lukasznowarkiewicz/3dCane/hardware-mechanical/accessories/uchwyt scienny do laski z miejscem na przewod do ladowania.png

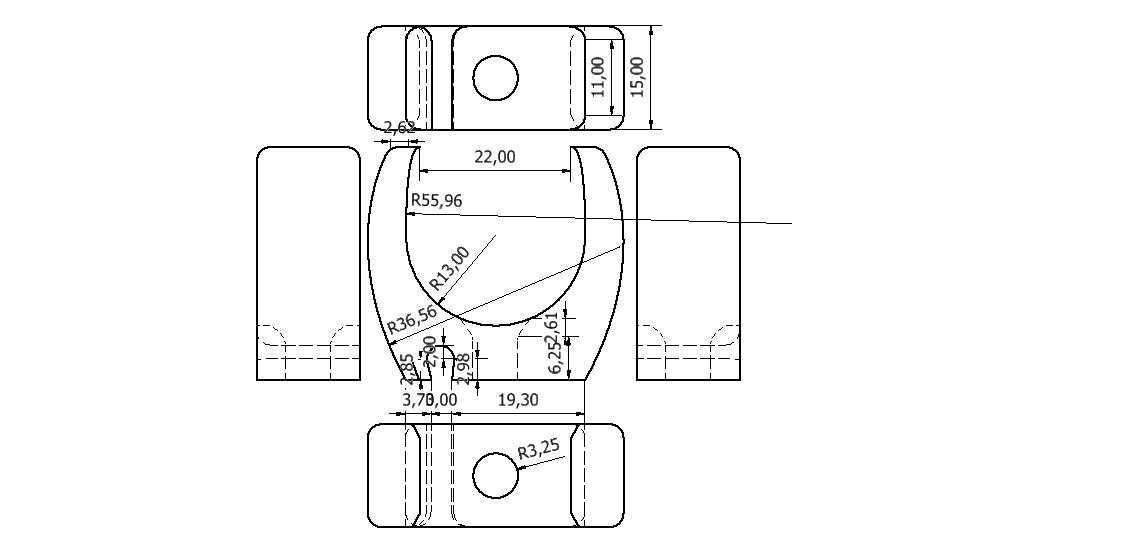
hardware-mechanical/accessories/uchwyt scienny do laski z miejscem na przewod do ladowania.png
