lukasznowarkiewicz/3dCane/hardware-mechanical/accessories/uchwyt scienny do laski.png

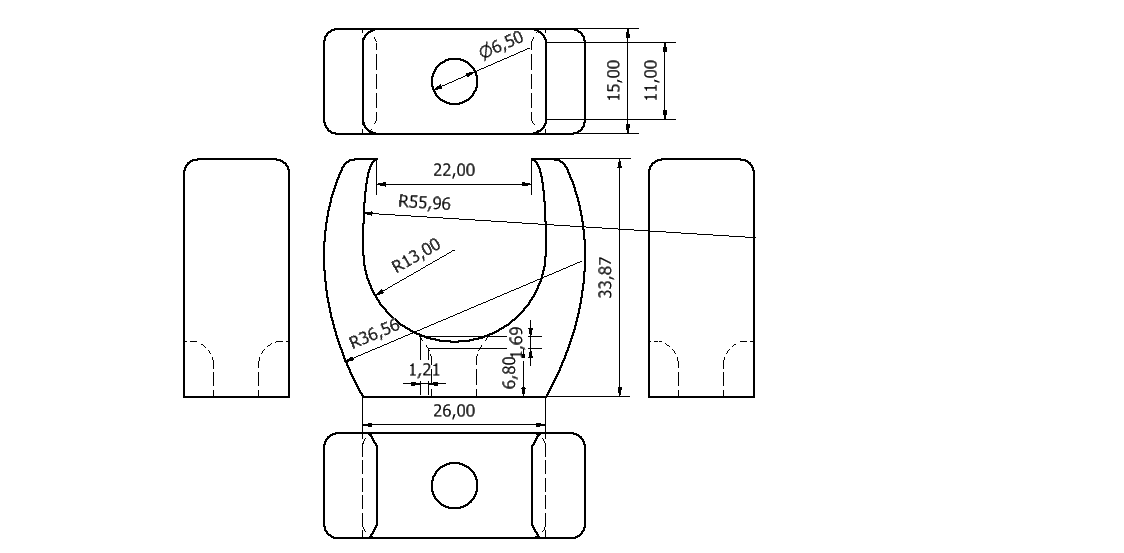
hardware-mechanical/accessories/uchwyt scienny do laski.png
