lukasznowarkiewicz/3dCane/hardware-mechanical/accessories/ˆadowarka usb v2 przykrywka.png

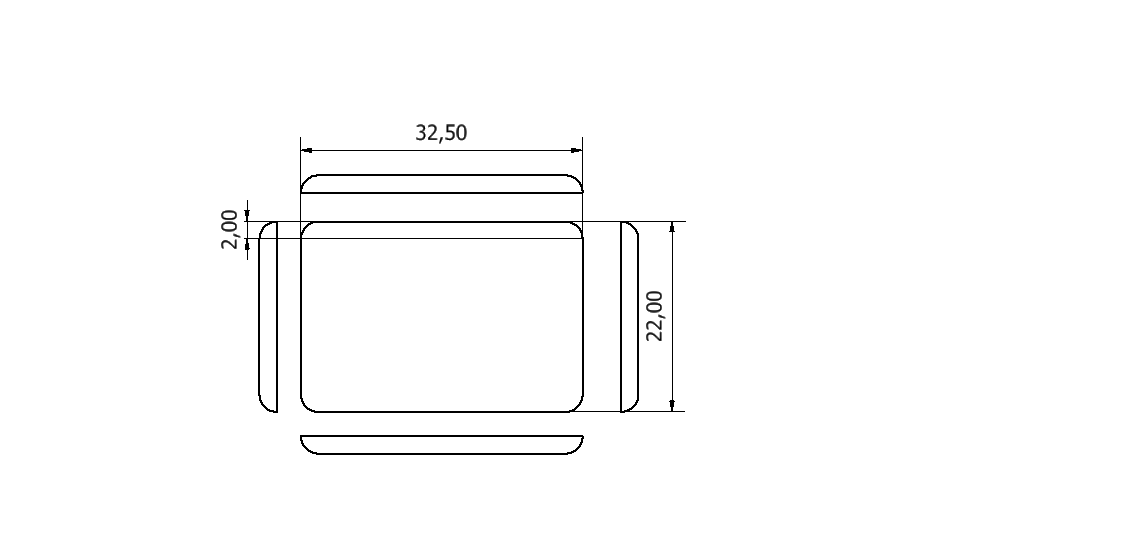
hardware-mechanical/accessories/ˆadowarka usb v2 przykrywka.png
