lukasznowarkiewicz/3dCane/hardware-mechanical/accessories/ˆadowarka usb v2-.png

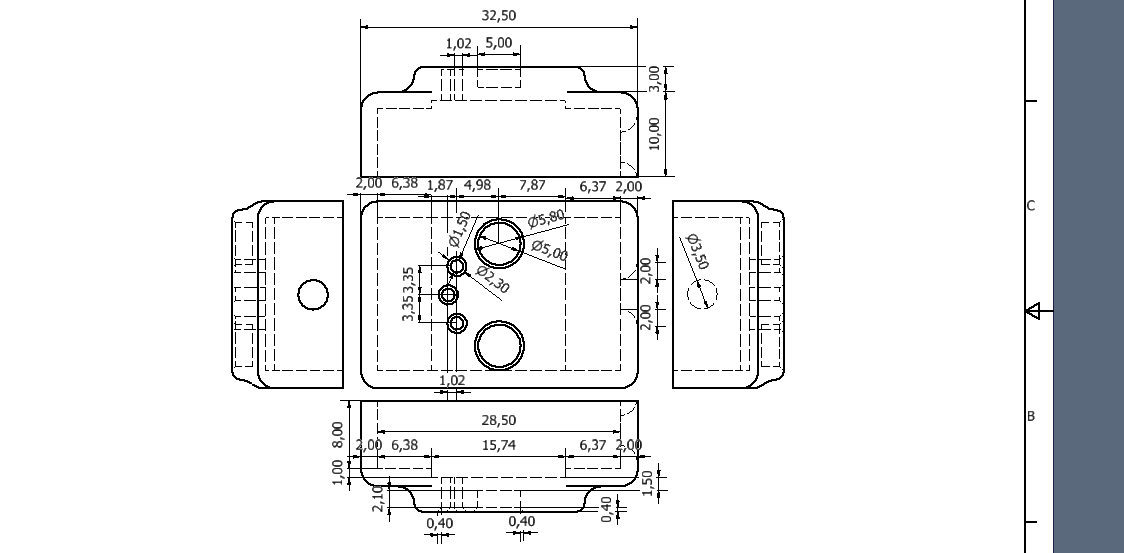
hardware-mechanical/accessories/ˆadowarka usb v2-.png
