lukasznowarkiewicz/3dCane/hardware-mechanical/cane/koncowka do laski - kula.png

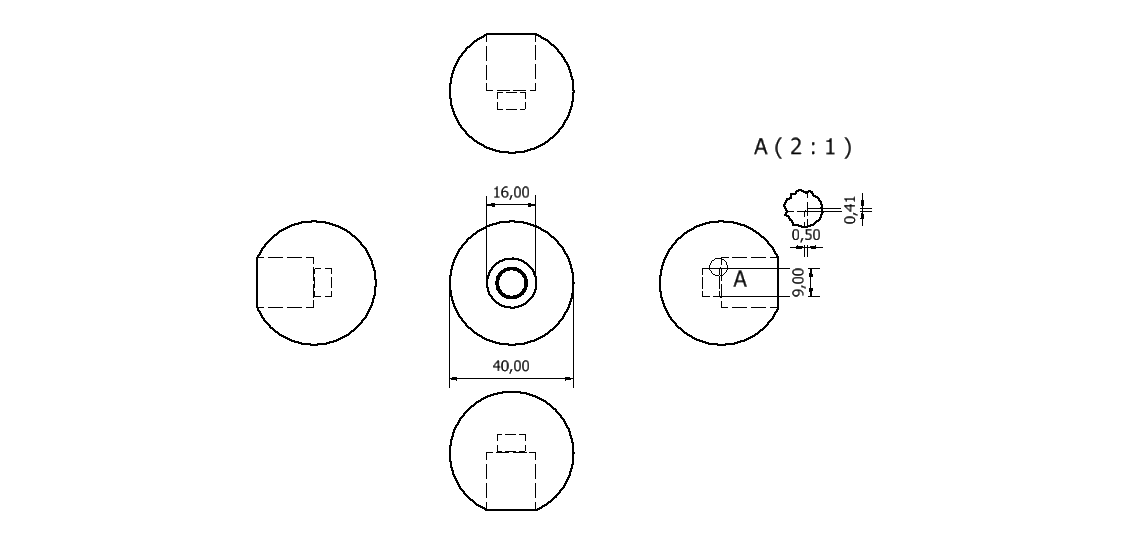
hardware-mechanical/cane/koncowka do laski - kula.png
