lukasznowarkiewicz/3dCane/hardware-mechanical/cane/koncowka z miejscem na magnes neodymowy 7x7x3.png

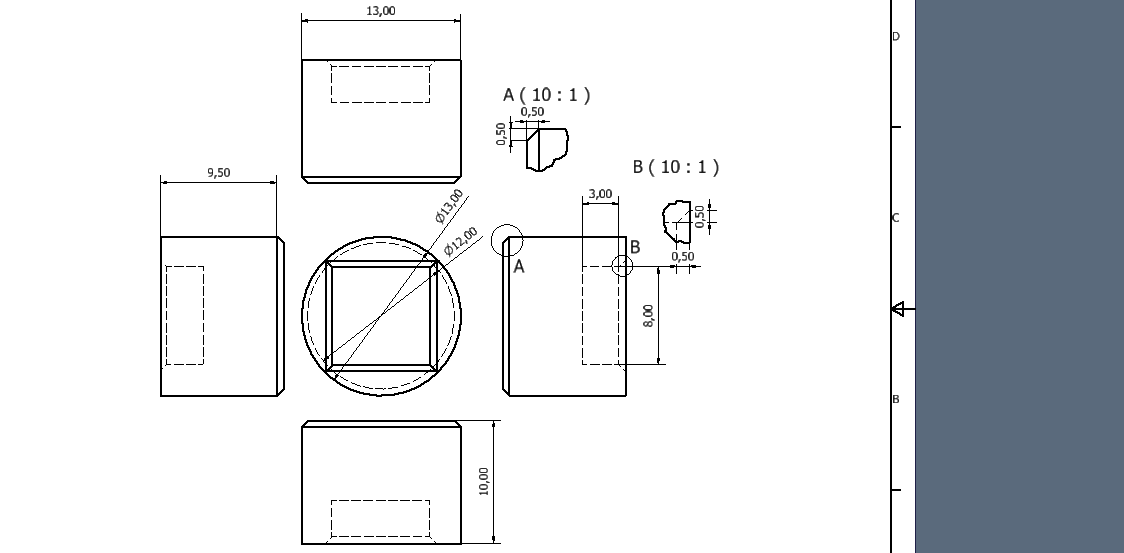
hardware-mechanical/cane/koncowka z miejscem na magnes neodymowy 7x7x3.png
