lukasznowarkiewicz/3dCane/hardware-mechanical/cane/obudowa do czujnikow odleglosci v3,2 - przykrywka.png

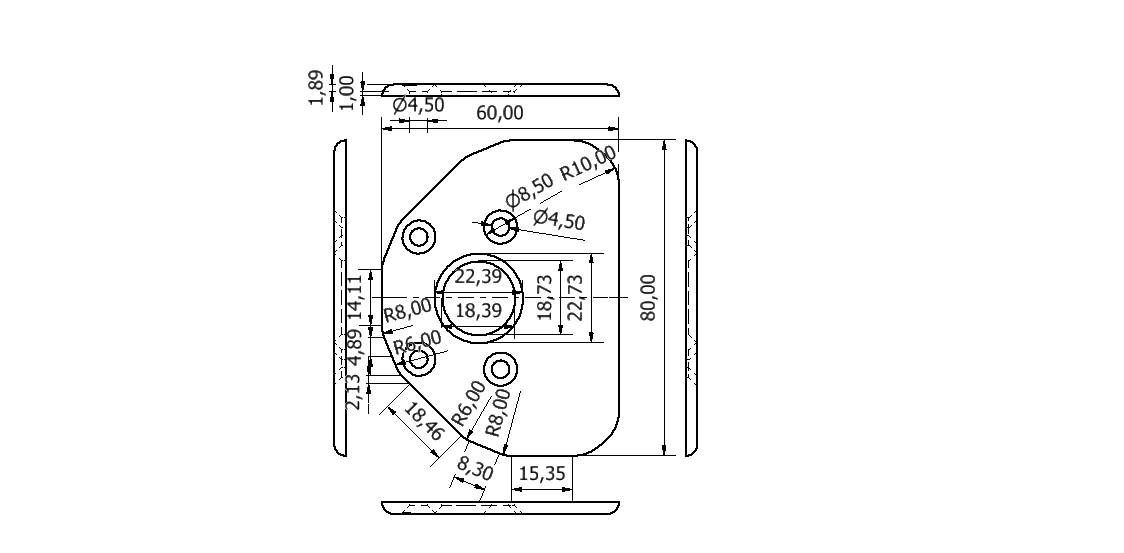
hardware-mechanical/cane/obudowa do czujnikow odleglosci v3,2 - przykrywka.png
