lukasznowarkiewicz/3dCane/hardware-mechanical/cane/obudowa do czujnikow odleglosci v3,2.bmp

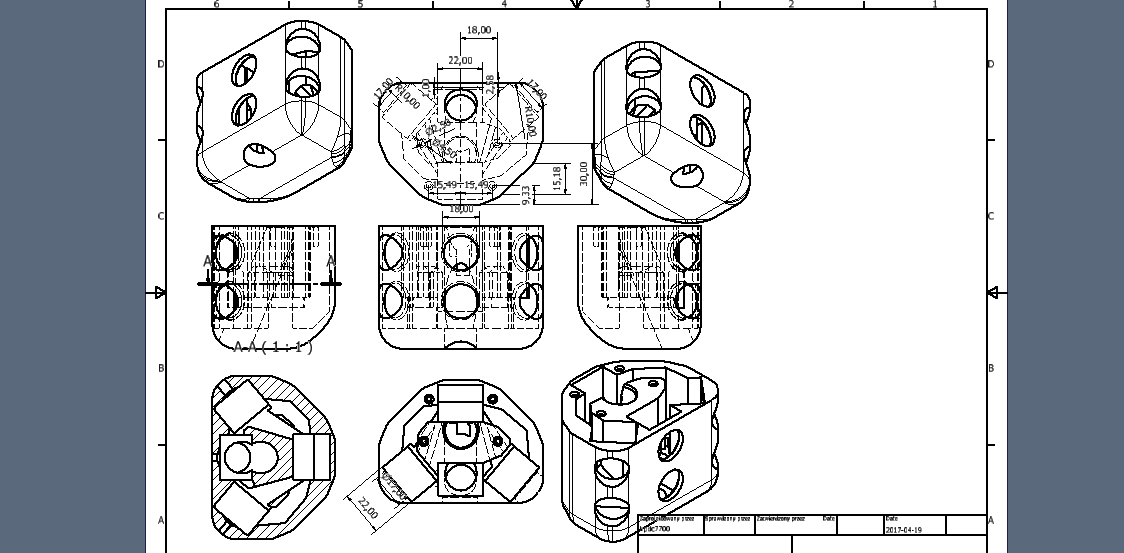
hardware-mechanical/cane/obudowa do czujnikow odleglosci v3,2.bmp
