lukasznowarkiewicz/3dCane/hardware-mechanical/cane/pierscien rurka cienka.png

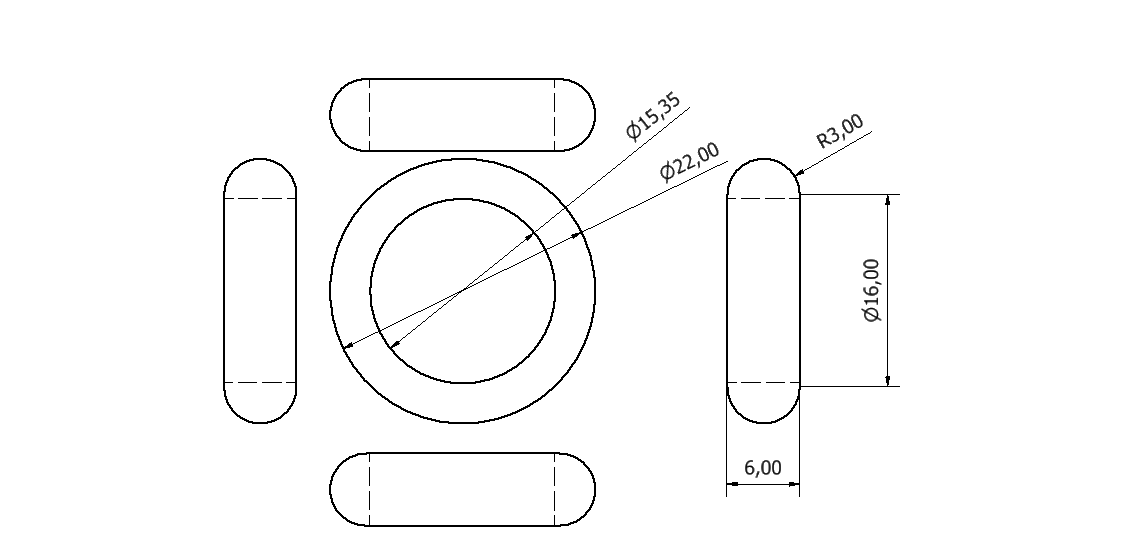
hardware-mechanical/cane/pierscien rurka cienka.png
