lukasznowarkiewicz/3dCane/hardware-mechanical/cane/raczka do laski ver 5.png

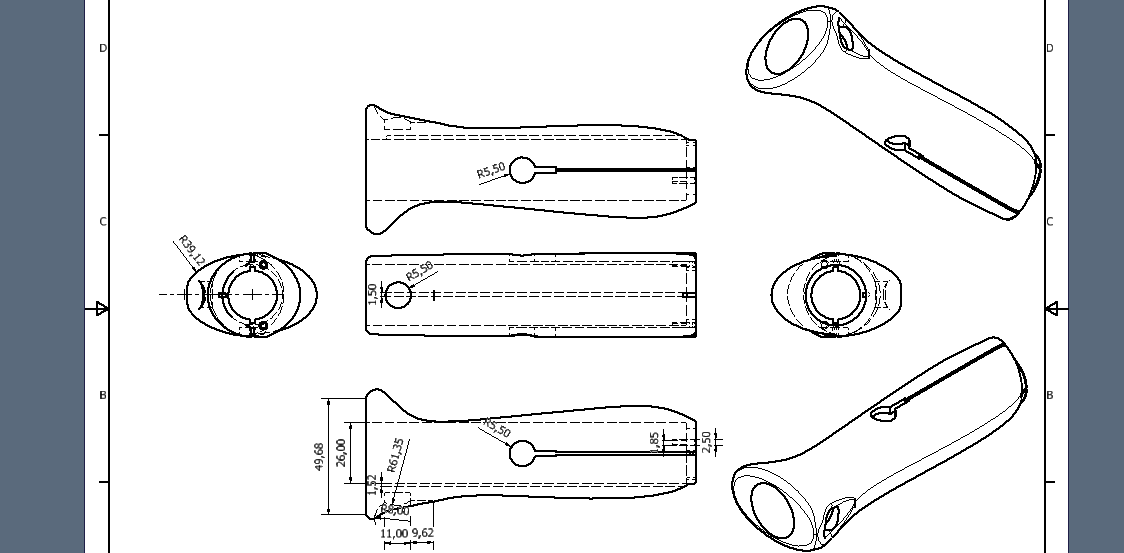
hardware-mechanical/cane/raczka do laski ver 5.png
