lukasznowarkiewicz/3dCane/hardware-mechanical/cane/zatyczka do raczki.png

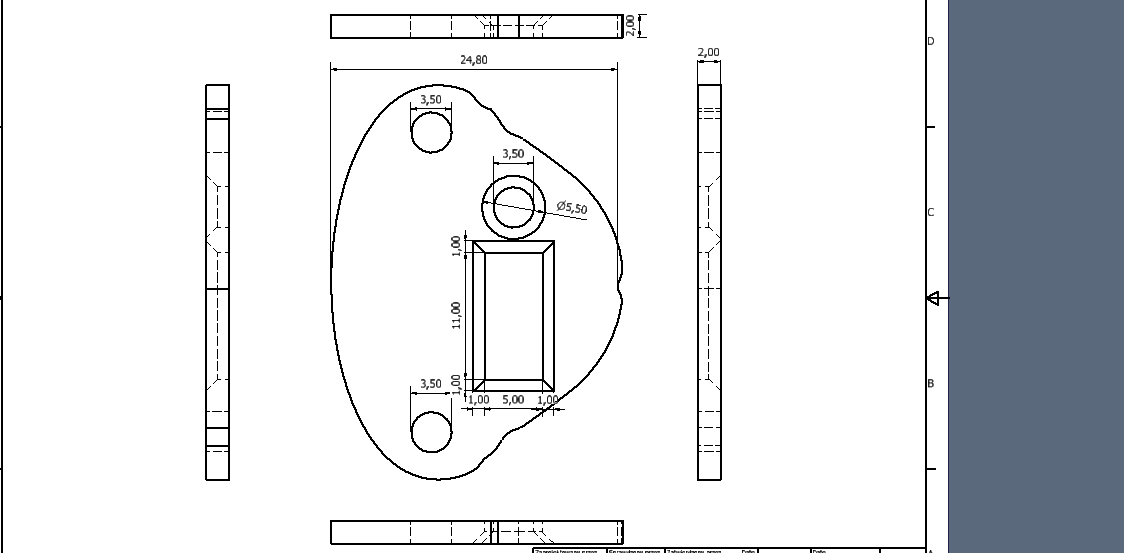
hardware-mechanical/cane/zatyczka do raczki.png
