lukasznowarkiewicz/3dCane/hardware-mechanical/screenshots/Screenshot_1.png

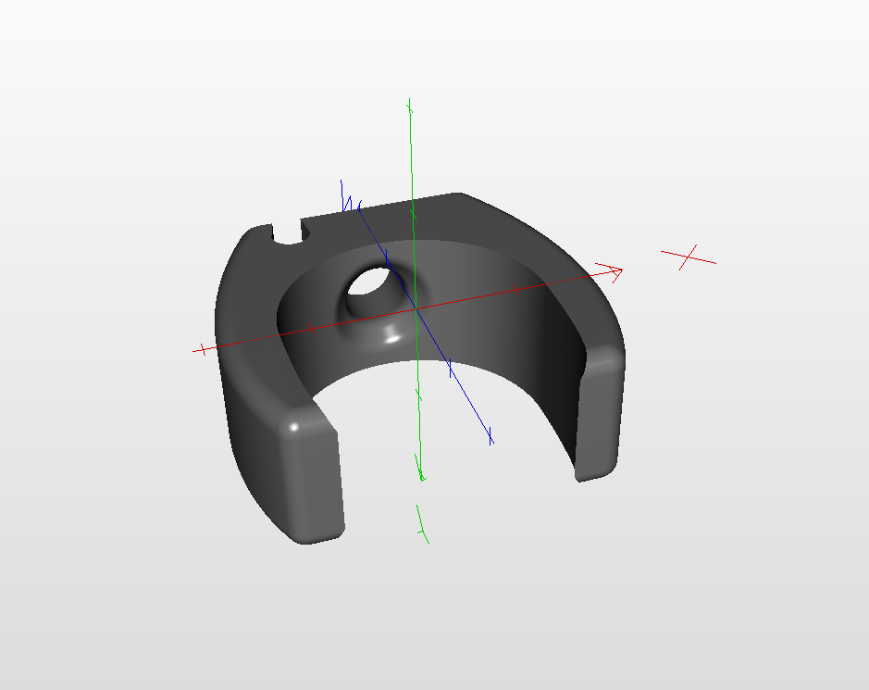
hardware-mechanical/screenshots/Screenshot_1.png
