lukasznowarkiewicz/3dCane/hardware-mechanical/screenshots/Screenshot_2.png

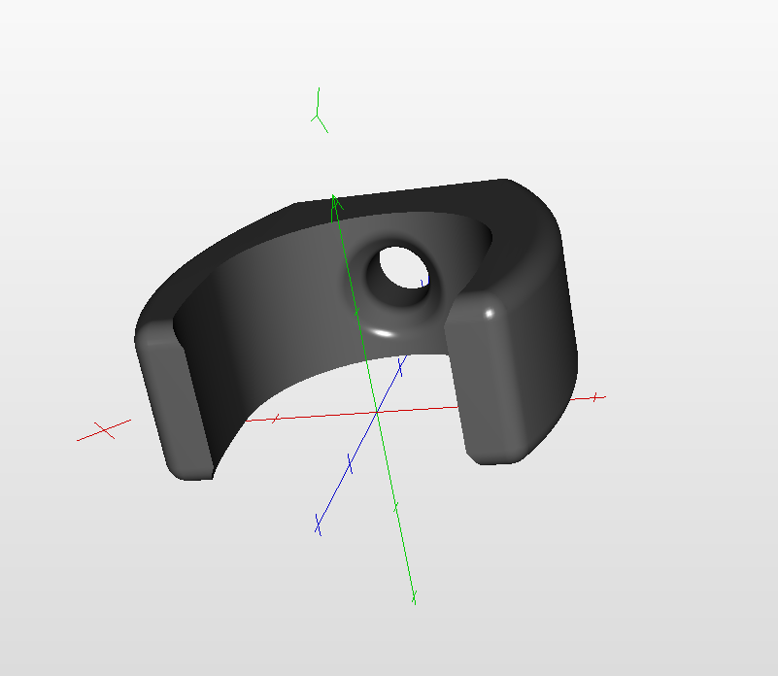
hardware-mechanical/screenshots/Screenshot_2.png
