lukasznowarkiewicz/3dCane/hardware-mechanical/screenshots/Screenshot_3.png

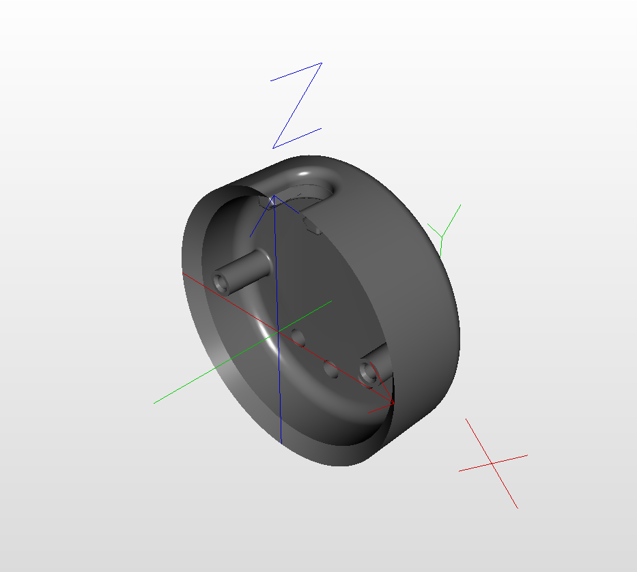
hardware-mechanical/screenshots/Screenshot_3.png
