lukasznowarkiewicz/3dCane/hardware-mechanical/screenshots/Screenshot_4.png

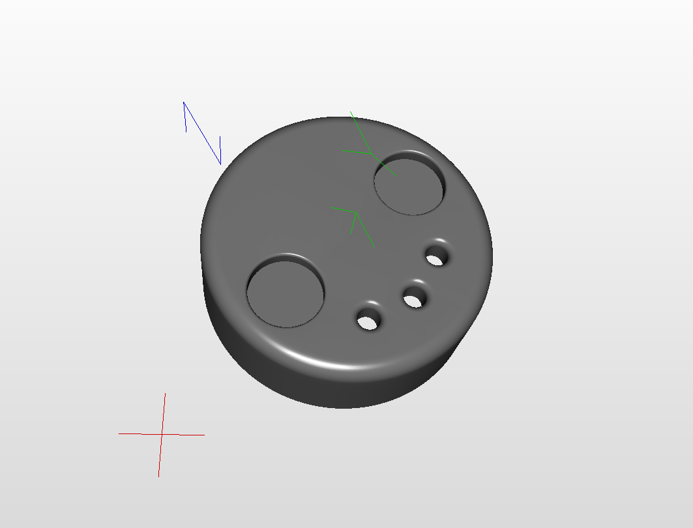
hardware-mechanical/screenshots/Screenshot_4.png
