lukasznowarkiewicz/3dCane/hardware-mechanical/screenshots/Screenshot_5.png

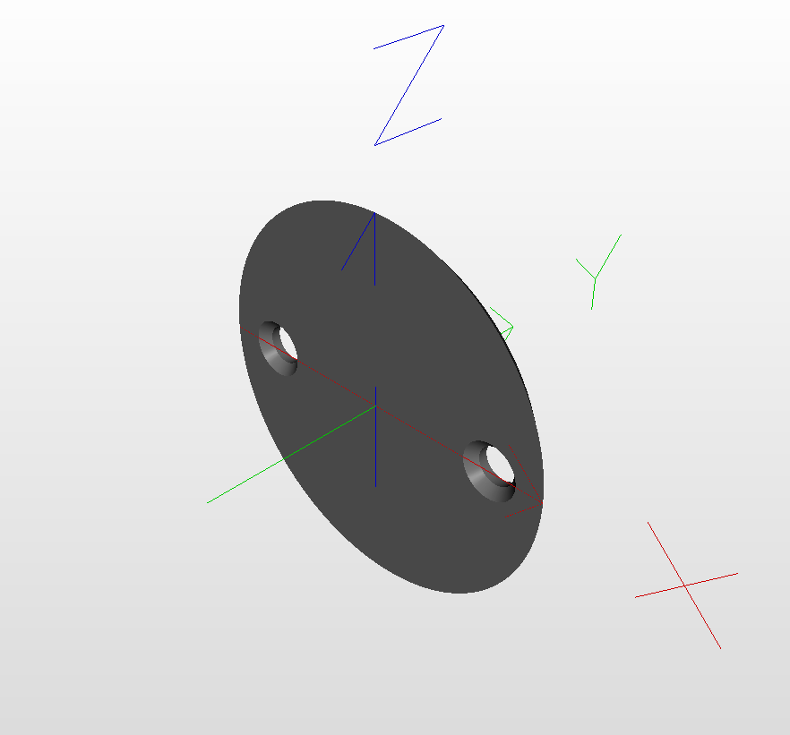
hardware-mechanical/screenshots/Screenshot_5.png
