lukasznowarkiewicz/3dCane/hardware-mechanical/screenshots/Screenshot_6.png

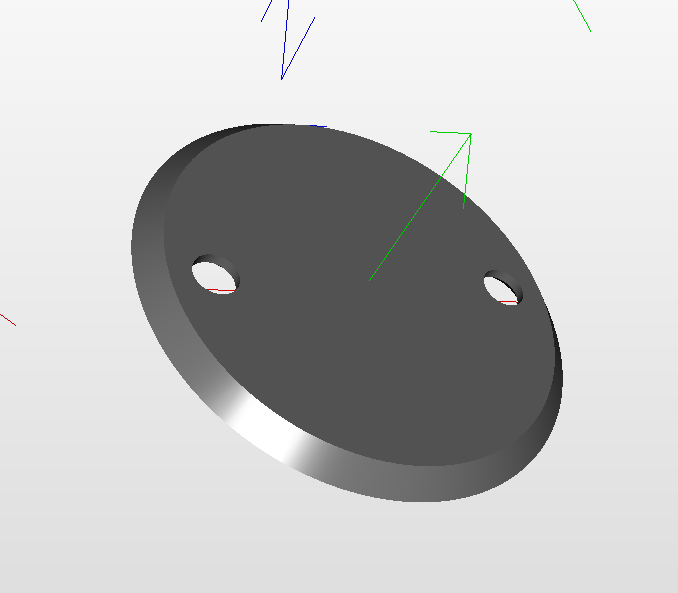
hardware-mechanical/screenshots/Screenshot_6.png
