lukasznowarkiewicz/3dCane/hardware-mechanical/screenshots/Screenshot_8.png

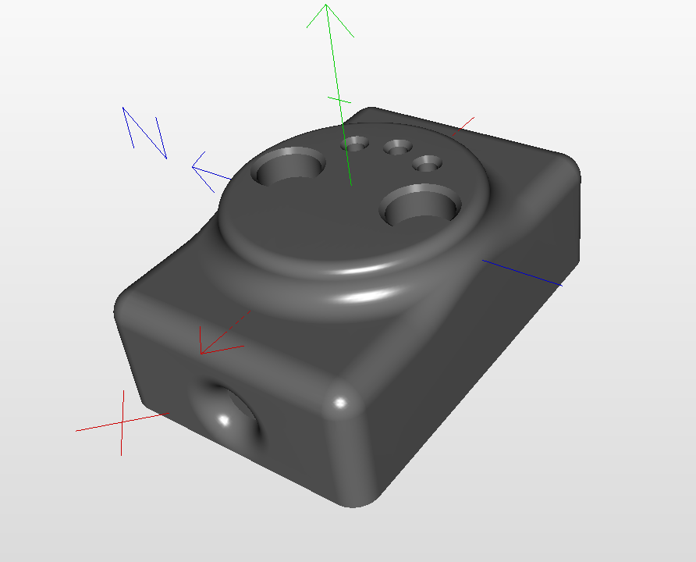
hardware-mechanical/screenshots/Screenshot_8.png
