lukasznowarkiewicz/3dCane/hardware-mechanical/screenshots/Screenshot_10.png

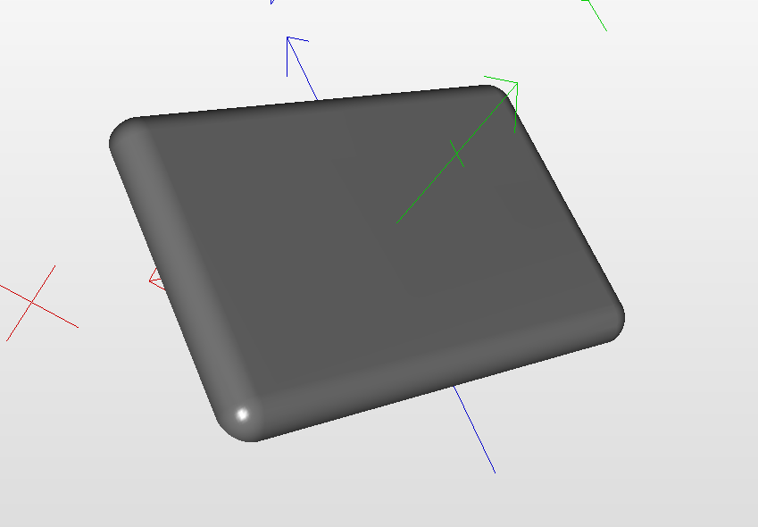
hardware-mechanical/screenshots/Screenshot_10.png
