lukasznowarkiewicz/3dCane/hardware-mechanical/screenshots/Screenshot_12.png

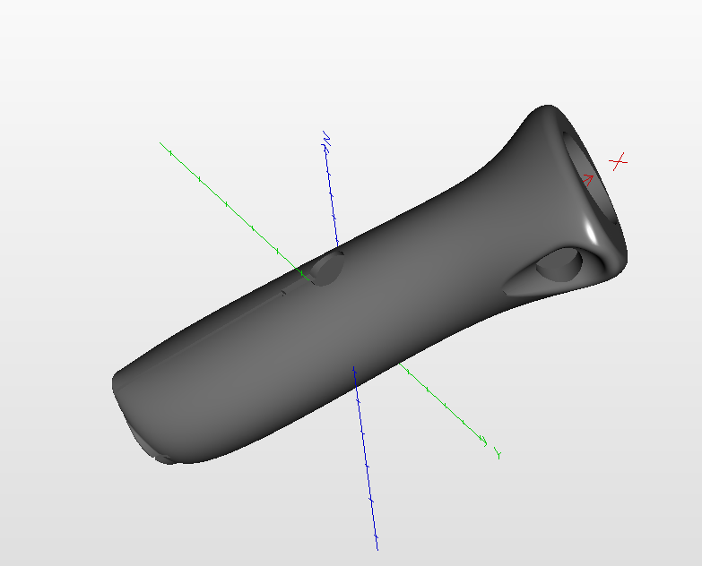
hardware-mechanical/screenshots/Screenshot_12.png
