lukasznowarkiewicz/3dCane/hardware-mechanical/screenshots/Screenshot_13.png

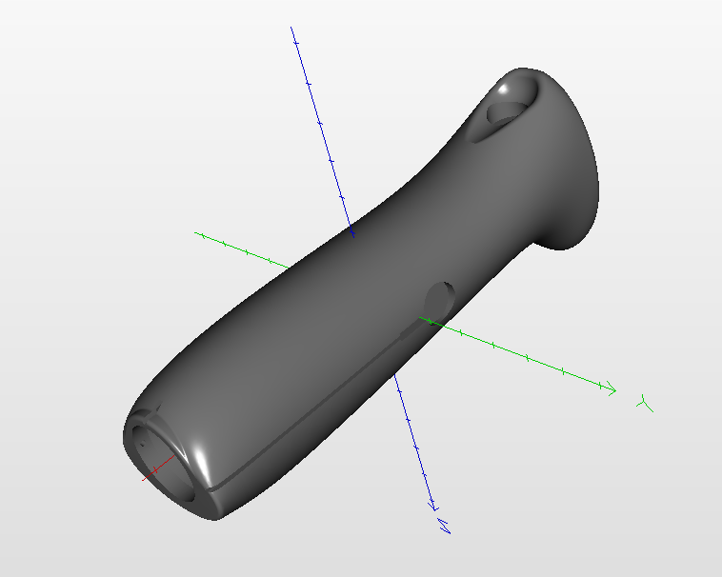
hardware-mechanical/screenshots/Screenshot_13.png
