lukasznowarkiewicz/3dCane/hardware-mechanical/screenshots/Screenshot_15.png

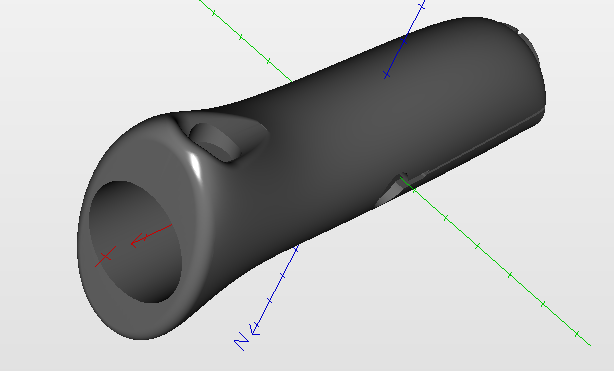
hardware-mechanical/screenshots/Screenshot_15.png
