lukasznowarkiewicz/3dCane/hardware-mechanical/screenshots/Screenshot_16.png

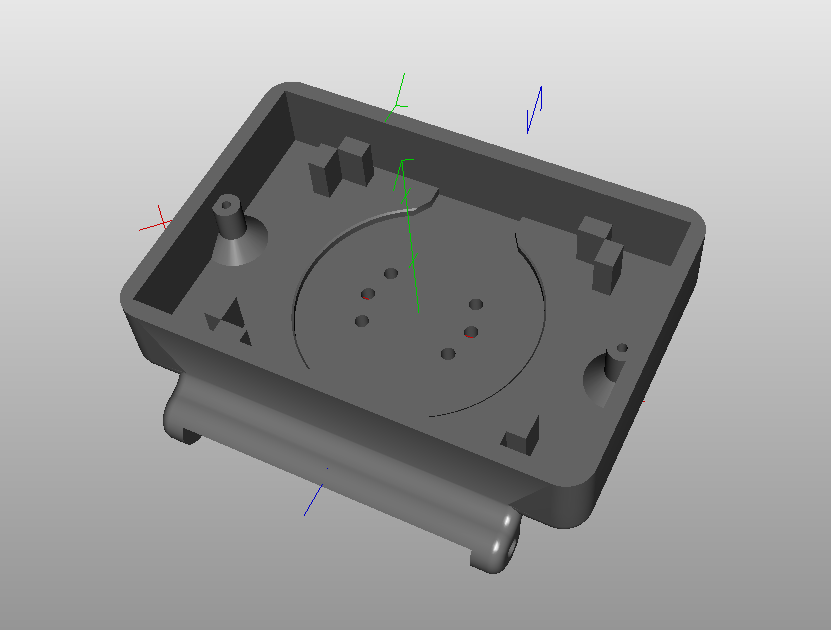
hardware-mechanical/screenshots/Screenshot_16.png
