lukasznowarkiewicz/3dCane/hardware-mechanical/screenshots/Screenshot_17.png

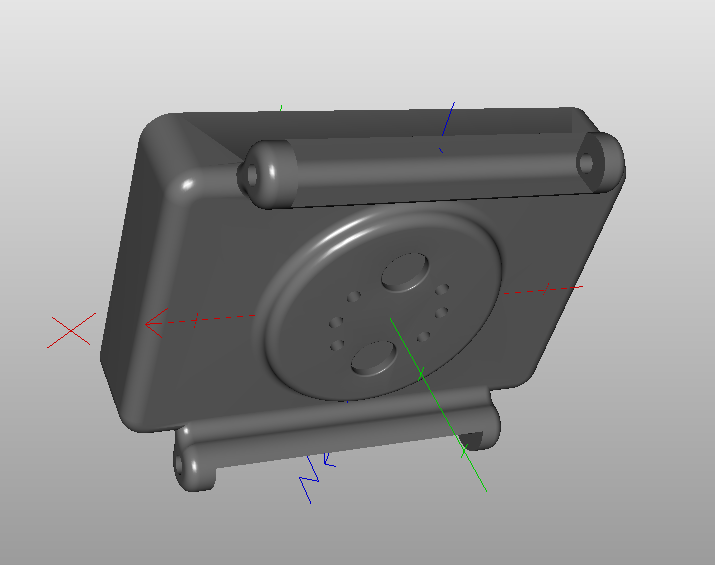
hardware-mechanical/screenshots/Screenshot_17.png
