lukasznowarkiewicz/3dCane/hardware-mechanical/screenshots/Screenshot_18.png

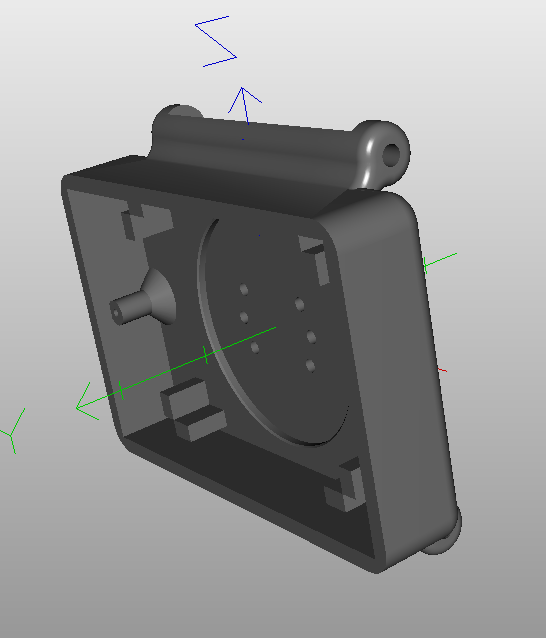
hardware-mechanical/screenshots/Screenshot_18.png
