lukasznowarkiewicz/3dCane/hardware-mechanical/screenshots/Screenshot_20.png

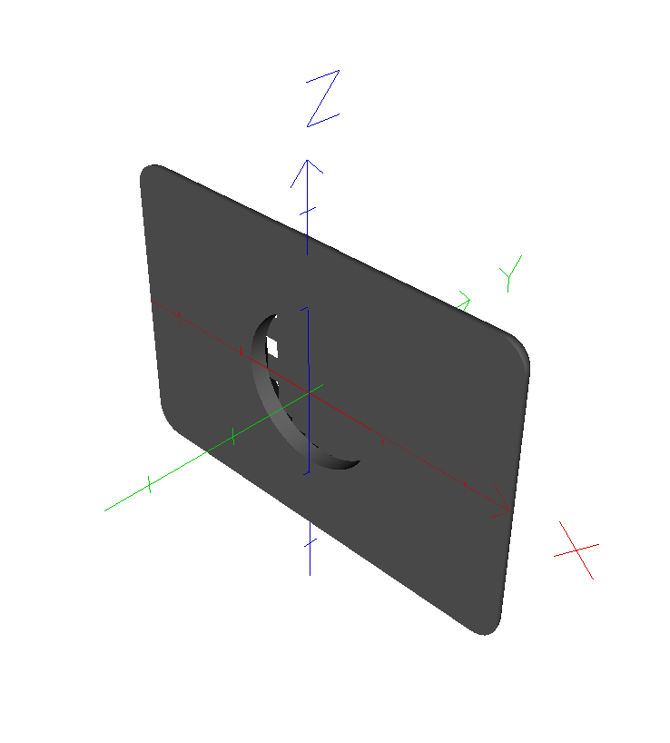
hardware-mechanical/screenshots/Screenshot_20.png
