lukasznowarkiewicz/3dCane/hardware-mechanical/screenshots/Screenshot_21.png

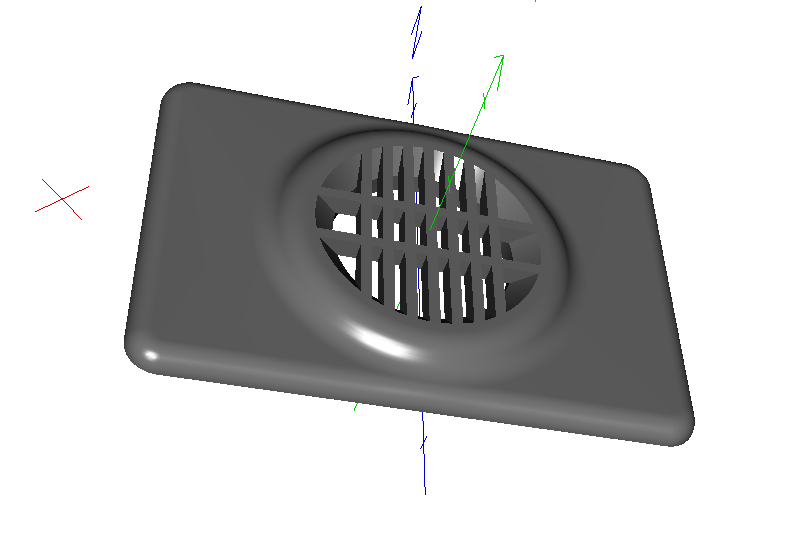
hardware-mechanical/screenshots/Screenshot_21.png
