lukasznowarkiewicz/3dCane/hardware-mechanical/screenshots/Screenshot_22.png

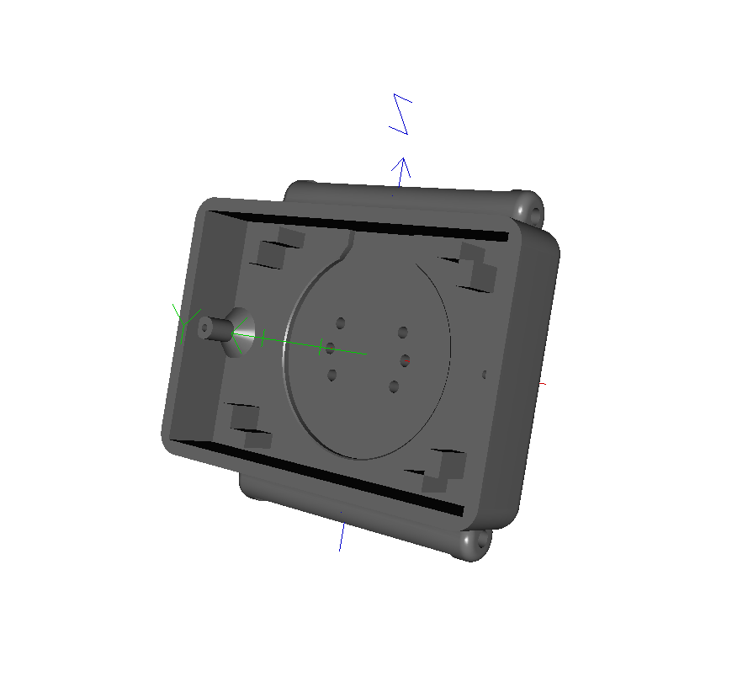
hardware-mechanical/screenshots/Screenshot_22.png
