lukasznowarkiewicz/3dCane/hardware-mechanical/screenshots/Screenshot_23.png

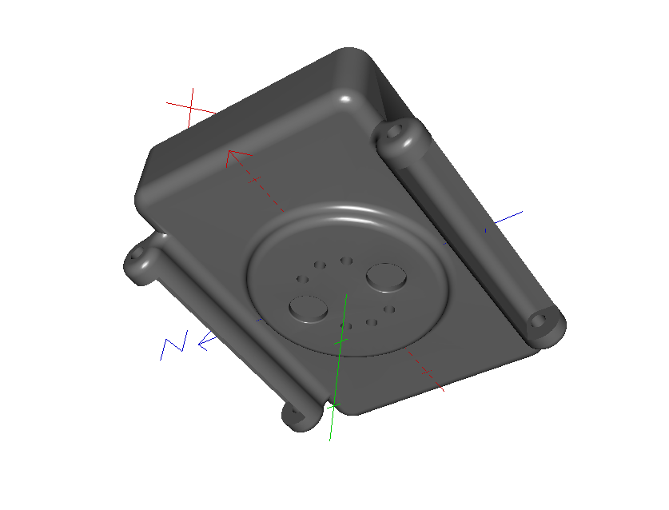
hardware-mechanical/screenshots/Screenshot_23.png
