lukasznowarkiewicz/3dCane/hardware-mechanical/screenshots/Screenshot_24.png

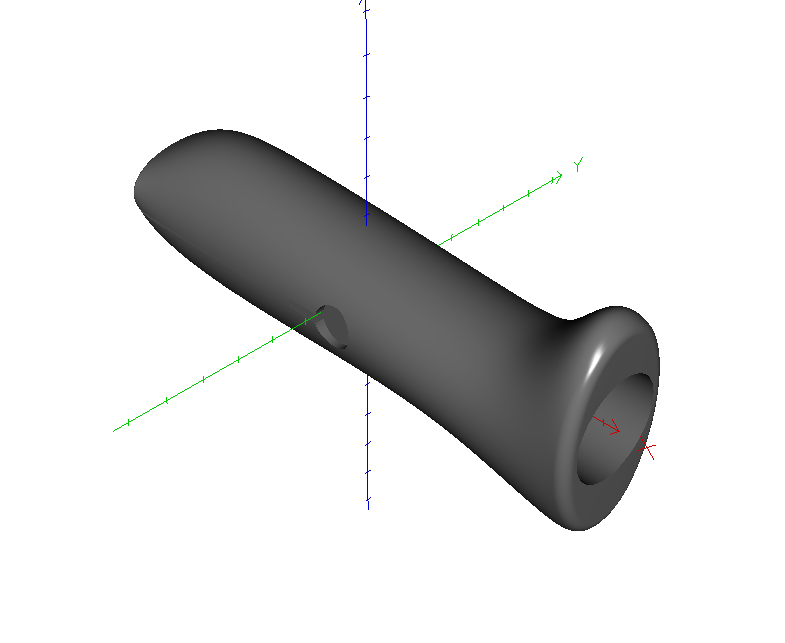
hardware-mechanical/screenshots/Screenshot_24.png
