lukasznowarkiewicz/3dCane/hardware-mechanical/screenshots/Screenshot_25.png

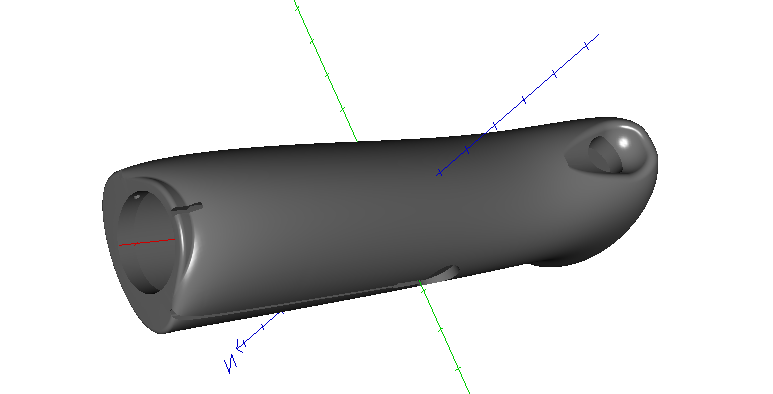
hardware-mechanical/screenshots/Screenshot_25.png
