lukasznowarkiewicz/3dCane/hardware-mechanical/screenshots/Screenshot_26.png

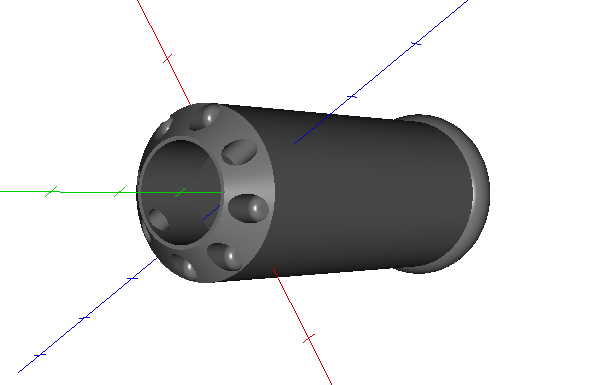
hardware-mechanical/screenshots/Screenshot_26.png
