lukasznowarkiewicz/3dCane/hardware-mechanical/screenshots/Screenshot_27.png

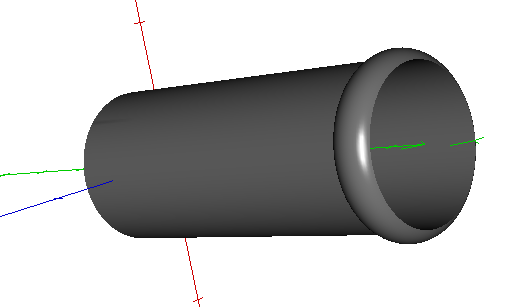
hardware-mechanical/screenshots/Screenshot_27.png
