lukasznowarkiewicz/3dCane/hardware-mechanical/screenshots/Screenshot_28.png

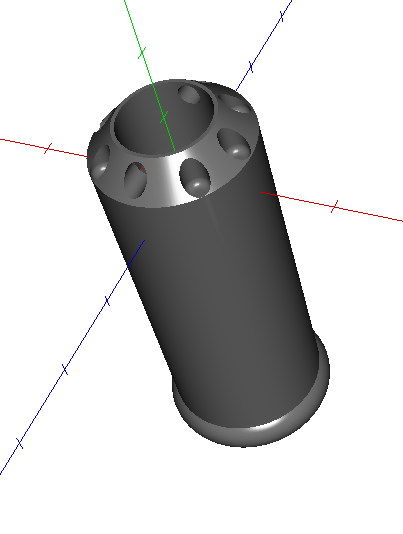
hardware-mechanical/screenshots/Screenshot_28.png
