lukasznowarkiewicz/3dCane/hardware-mechanical/watch/obudowa zegarka gขra rev2,2.bmp

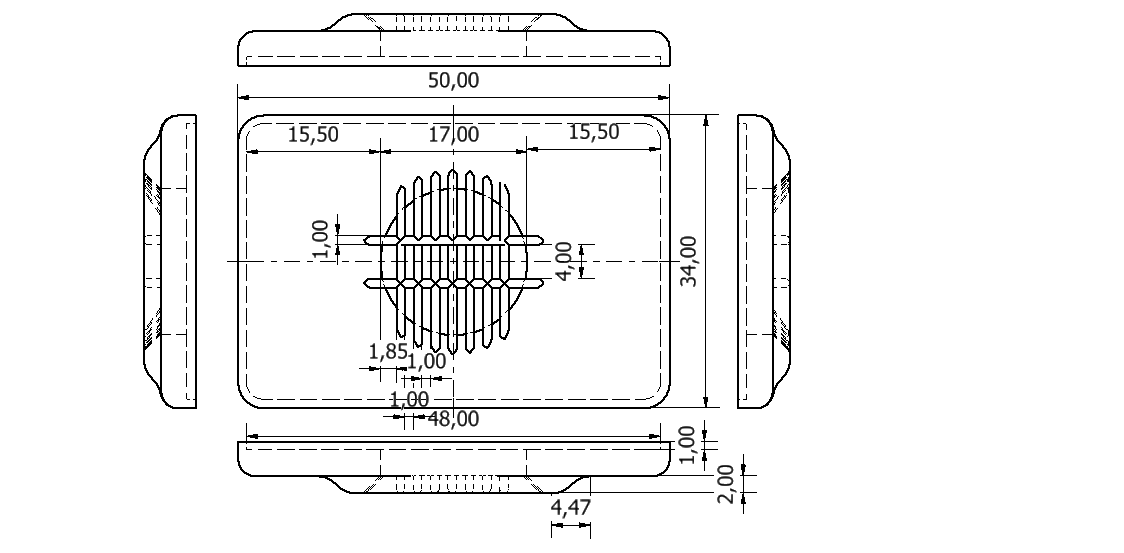
hardware-mechanical/watch/obudowa zegarka gขra rev2,2.bmp
