lukasznowarkiewicz/3dCane/imagesAndVideos/block_diagram_cane.jpg

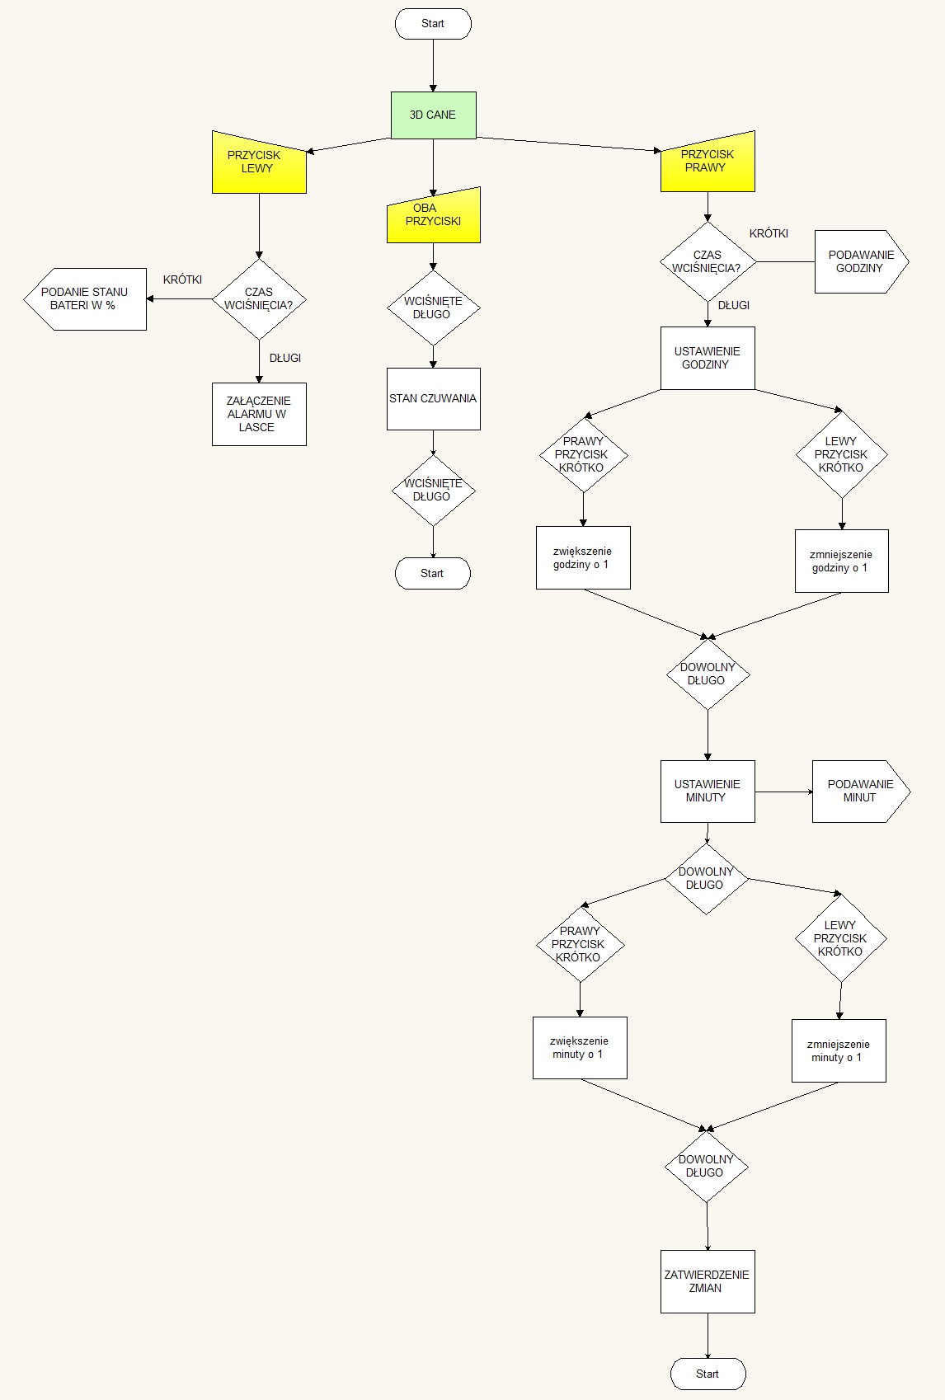
imagesAndVideos/block_diagram_cane.jpg
