lukasznowarkiewicz/3dCane/imagesAndVideos/cane_low_PCB.jpg

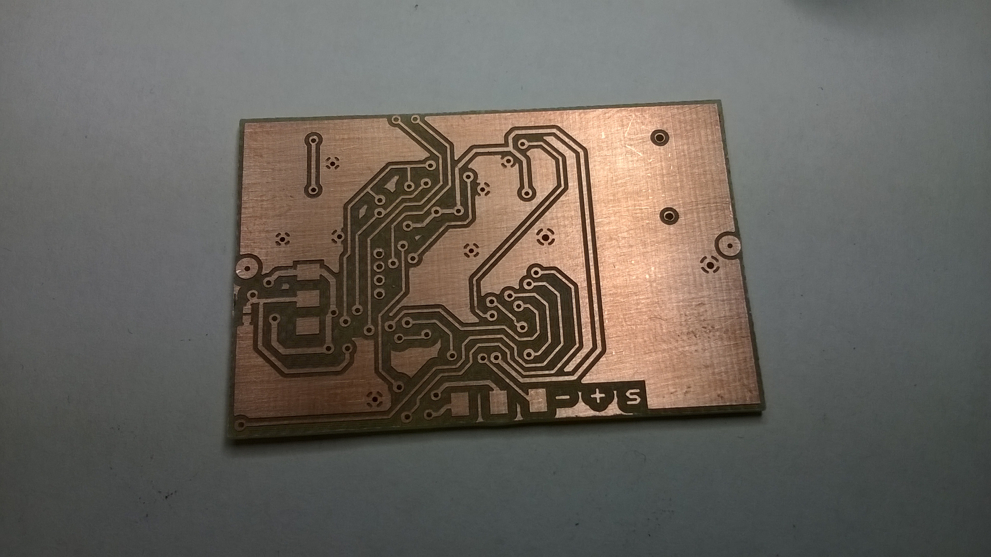
imagesAndVideos/cane_low_PCB.jpg
