lukasznowarkiewicz/3dCane/imagesAndVideos/funkcje zegarka.jpg

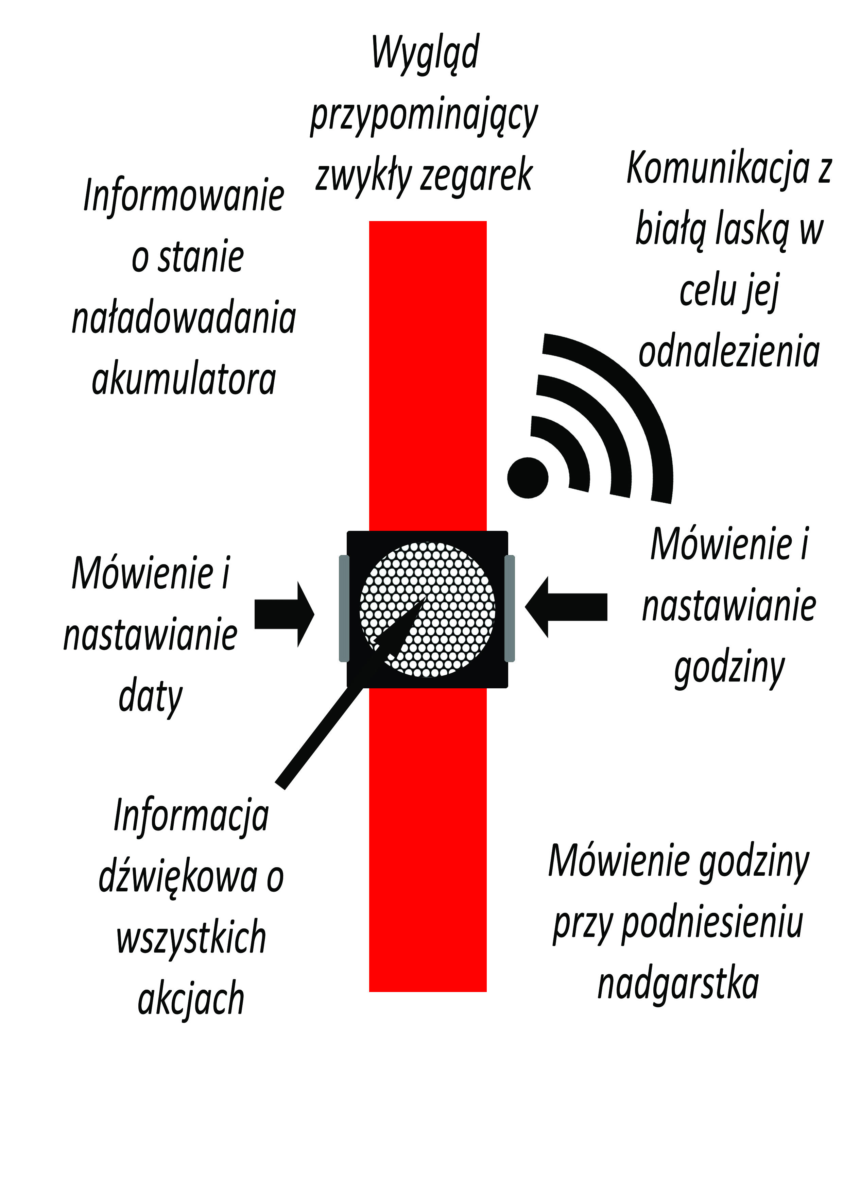
imagesAndVideos/funkcje zegarka.jpg
