lukasznowarkiewicz/3dCane/imagesAndVideos/IMG_0590.JPG

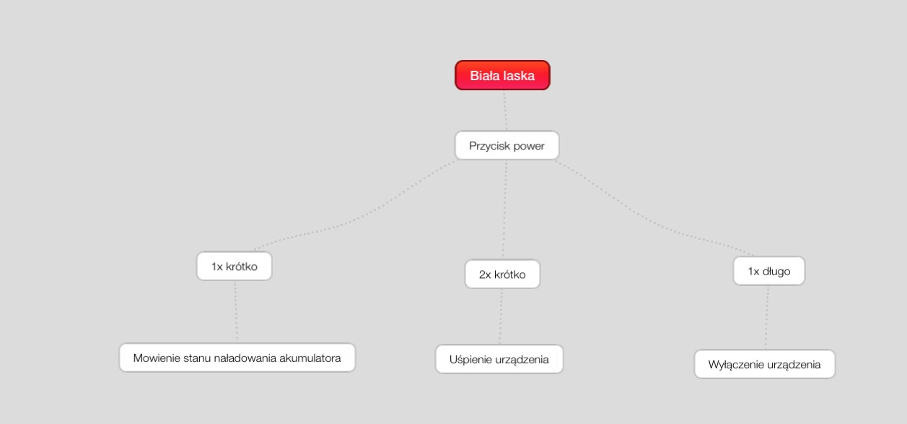
imagesAndVideos/IMG_0590.JPG
