lukasznowarkiewicz/3dCane/imagesAndVideos/IMG_0591.JPG

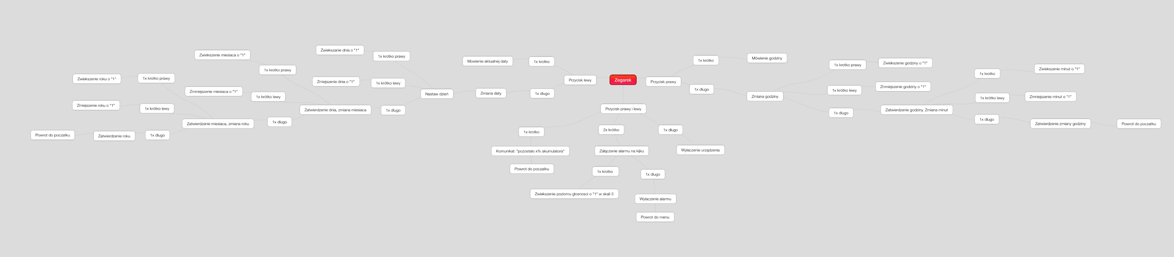
imagesAndVideos/IMG_0591.JPG
