lukasznowarkiewicz/3dCane/imagesAndVideos/inventor.png

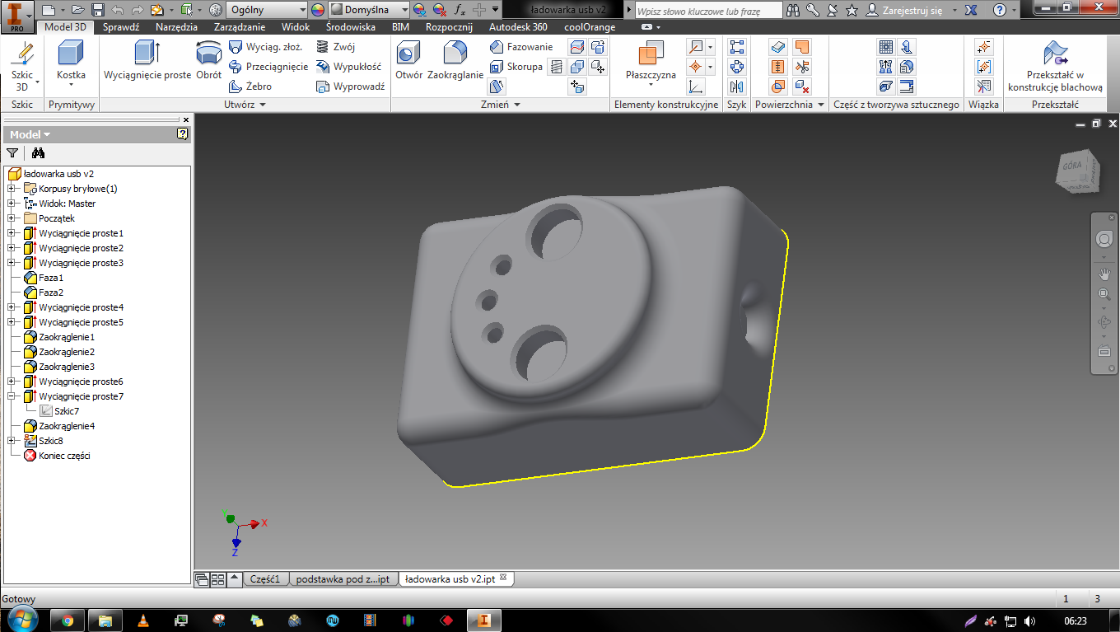
imagesAndVideos/inventor.png
