lukasznowarkiewicz/3dCane/imagesAndVideos/pcb_with_diy_vias.jpg

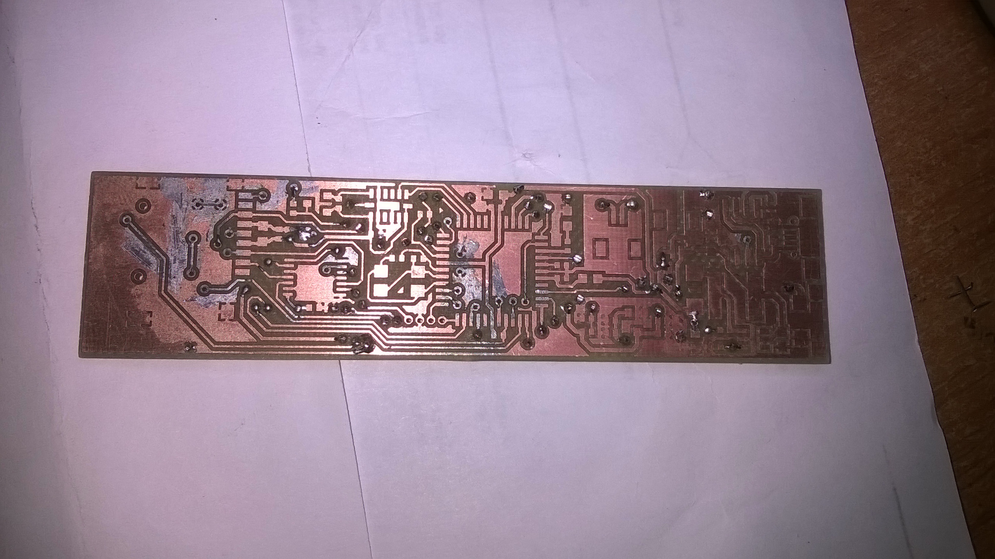
imagesAndVideos/pcb_with_diy_vias.jpg
