lukasznowarkiewicz/3dCane/imagesAndVideos/trophy.JPG

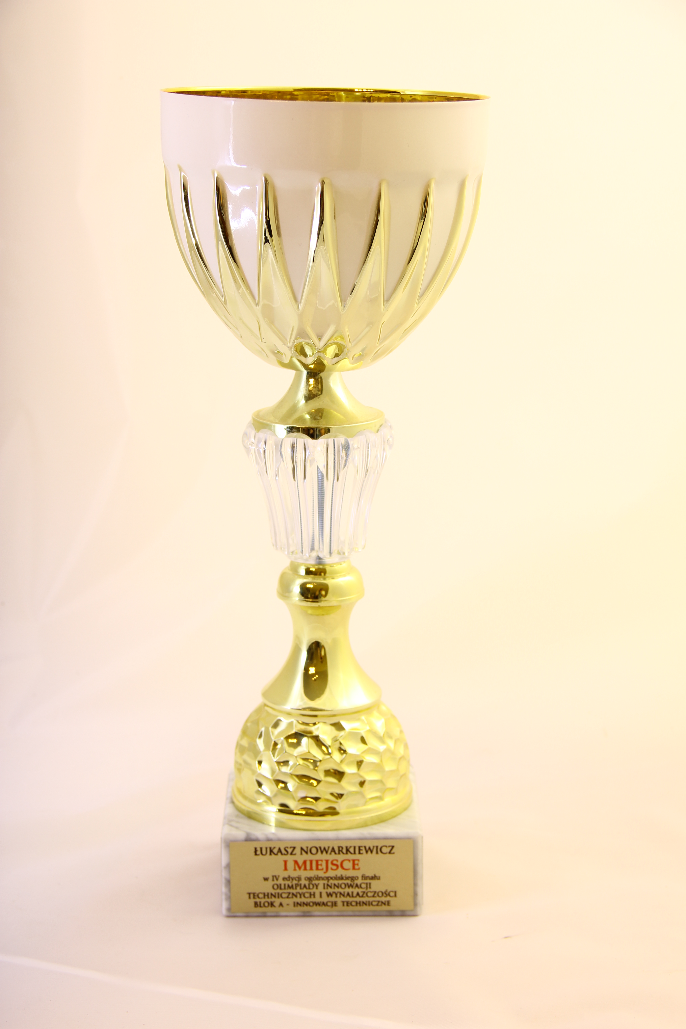
imagesAndVideos/trophy.JPG
