lukasznowarkiewicz/3dCane/imagesAndVideos/wrist_watch_charger.JPG

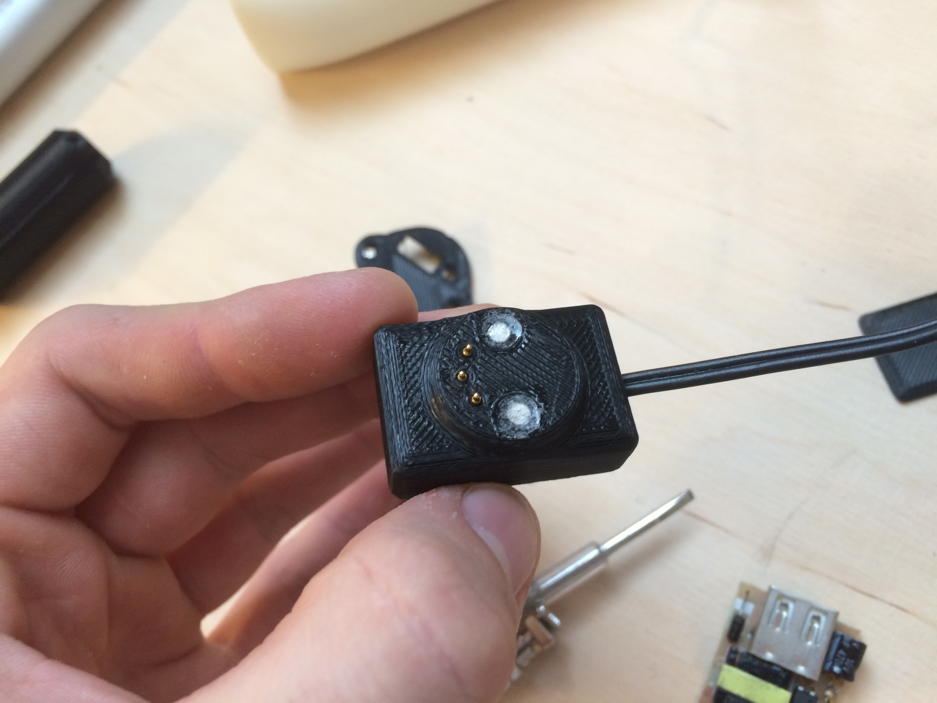
imagesAndVideos/wrist_watch_charger.JPG
