lukasznowarkiewicz/3dCane/hardware-mechanical/accessories/logo e-laska 1.stl

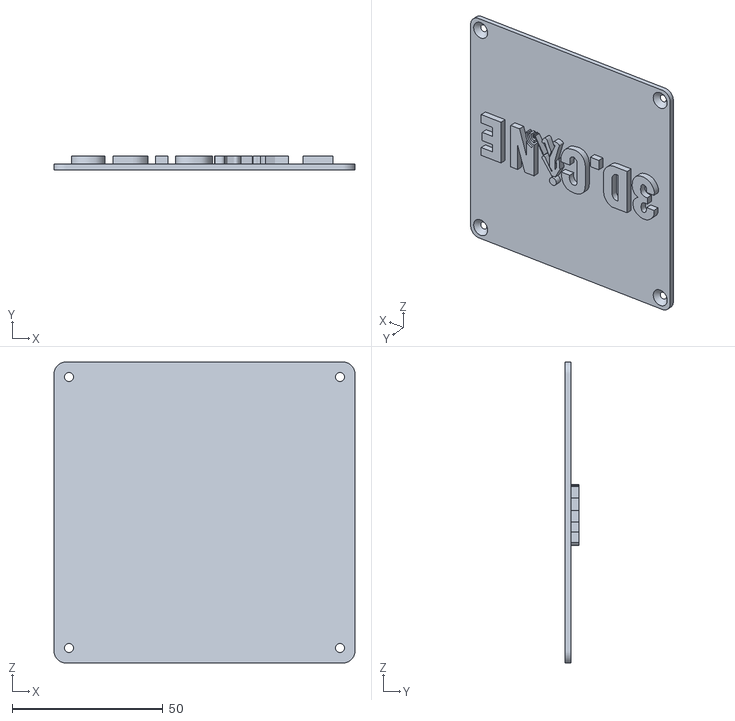
[picture p88: CAD file, 2024-03-30]
hardware-mechanical/accessories/logo e-laska 1.stl
100.0 x 4.65 x 100.0
