lukasznowarkiewicz/3dCane/hardware-mechanical/cane/obudowa do czujnikow odleglosci v3,2.stl

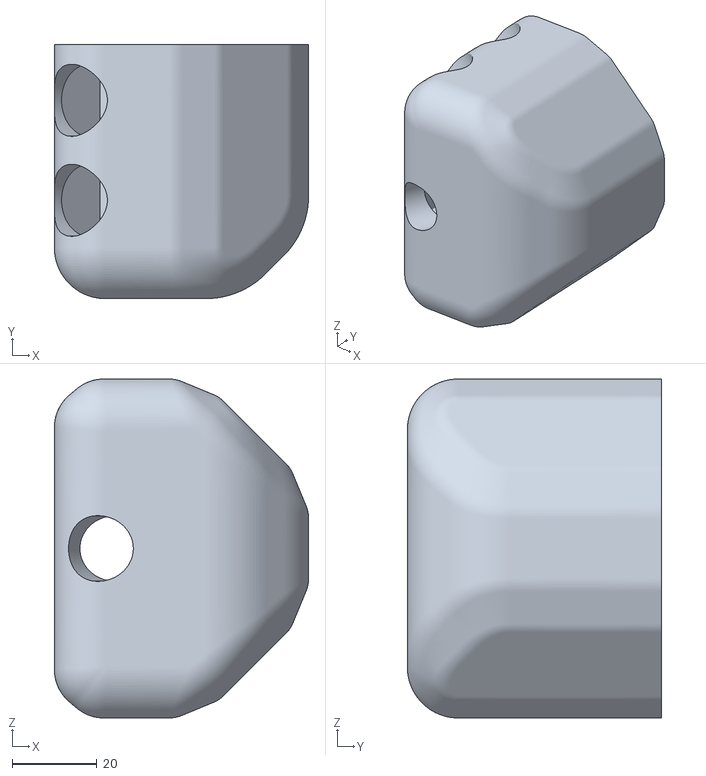
[picture p89: CAD file, 2024-03-30]
hardware-mechanical/cane/obudowa do czujnikow odleglosci v3,2.stl
60.0 x 60.0 x 80.0
