lukasznowarkiewicz/3dCane/hardware-mechanical/cane/koncowka do laski - walec zaokraglony.stl

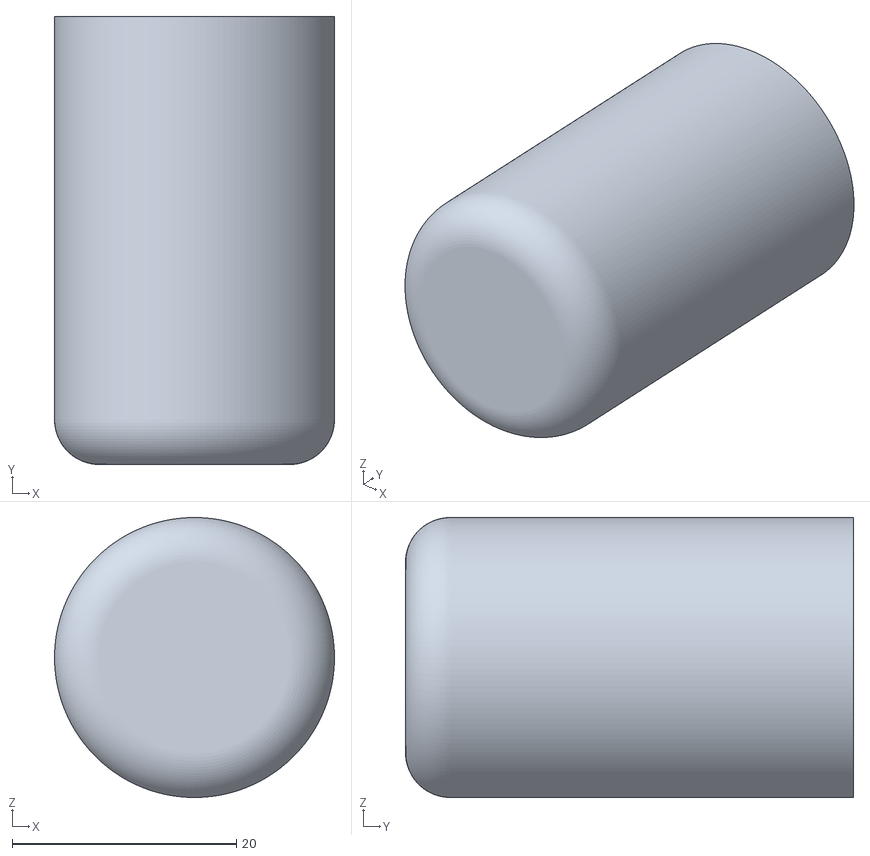
[picture p90: CAD file, 2024-03-30]
hardware-mechanical/cane/koncowka do laski - walec zaokraglony.stl
25.0 x 40.0 x 25.0
