lukasznowarkiewicz/3dCane/hardware-mechanical/cane/raczka do laski ver 5,2.stl

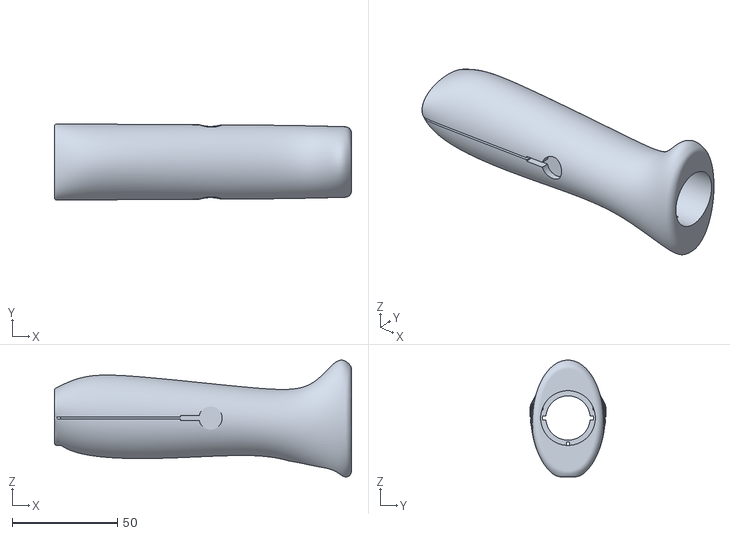
[picture p91: CAD file, 2024-03-30]
hardware-mechanical/cane/raczka do laski ver 5,2.stl
141.1 x 36.2 x 55.5
