lukasznowarkiewicz/3dCane/hardware-mechanical/cane/TRZYMACZ PCB 5mm.stl

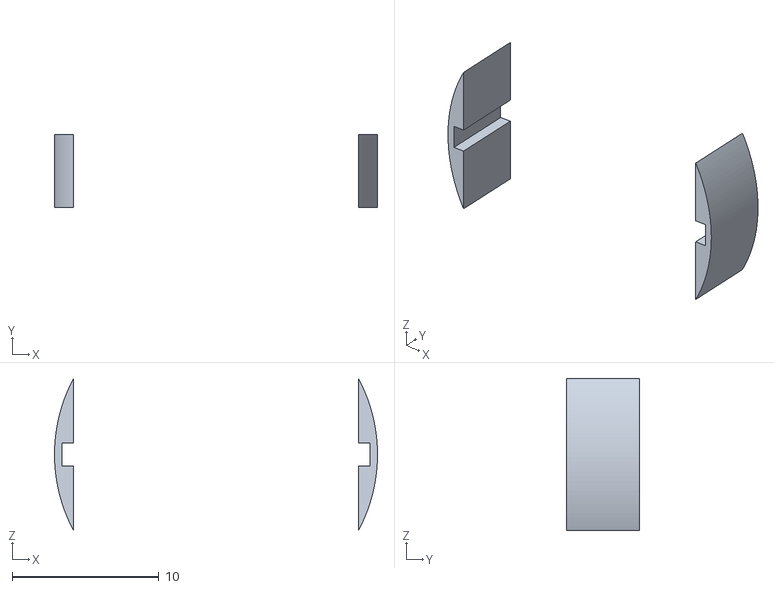
[picture p92: CAD file, 2024-03-30]
hardware-mechanical/cane/TRZYMACZ PCB 5mm.stl
22.0 x 5.00 x 10.4
