lukasznowarkiewicz/3dCane/hardware-mechanical/cane/koncowka do laski - kula.stl

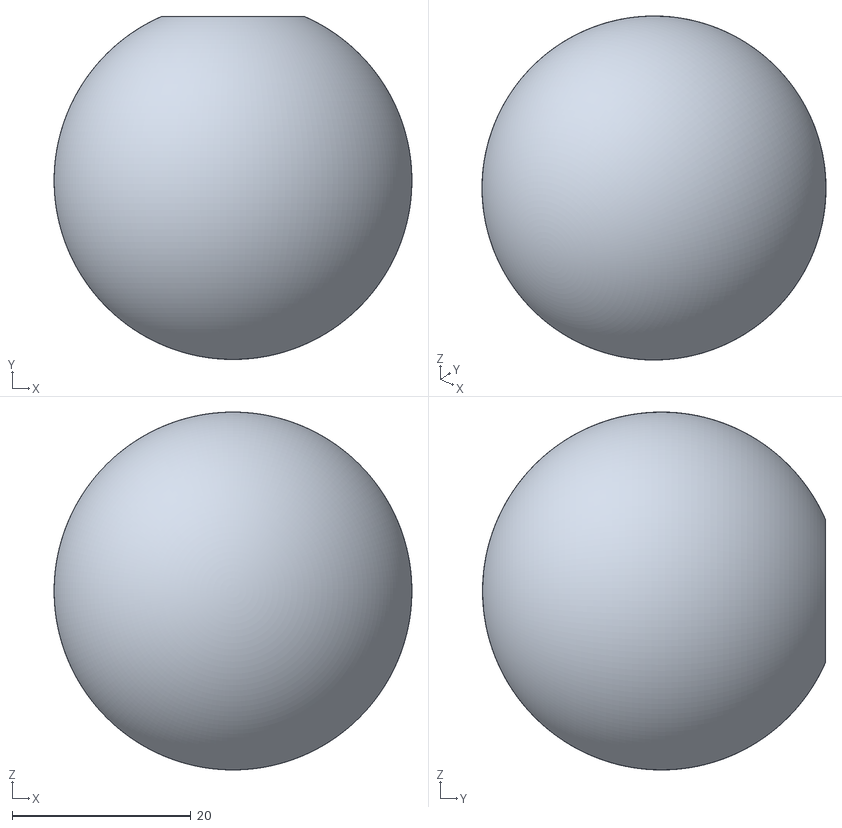
[picture p93: CAD file, 2024-03-30]
hardware-mechanical/cane/koncowka do laski - kula.stl
40.0 x 38.3 x 40.0
