lukasznowarkiewicz/3dCane/hardware-mechanical/cane/zatyczka do raczki.stl

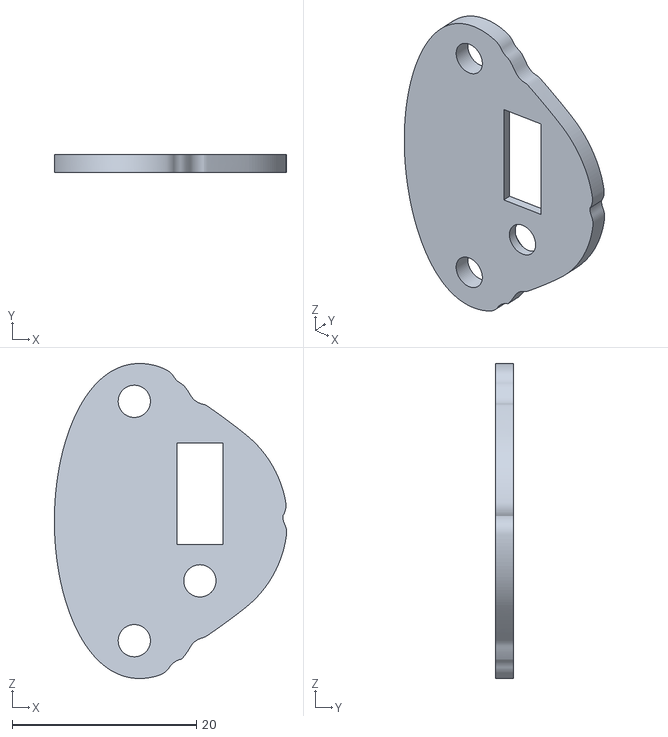
[picture p94: CAD file, 2024-03-30]
hardware-mechanical/cane/zatyczka do raczki.stl
25.2 x 2.00 x 34.2
