lukasznowarkiewicz/3dCane/hardware-mechanical/cane/pierscien nr 1 gorny v3.stl

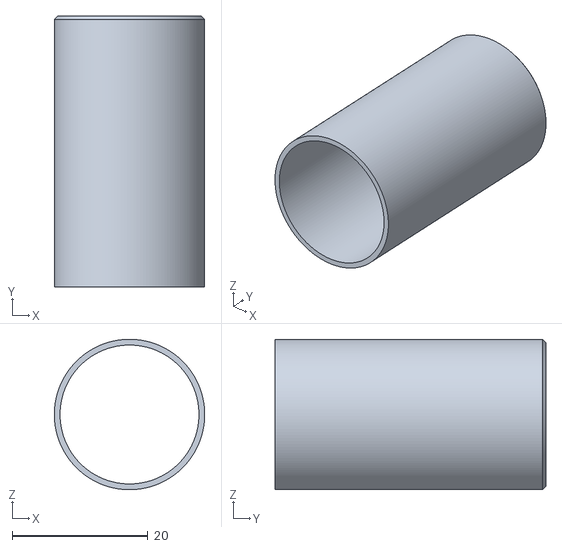
[picture p95: CAD file, 2024-03-30]
hardware-mechanical/cane/pierscien nr 1 gorny v3.stl
22.2 x 40.0 x 22.2
