lukasznowarkiewicz/3dCane/hardware-mechanical/cane/koncowka z miejscem na magnes neodymowy 7x7x3.stl

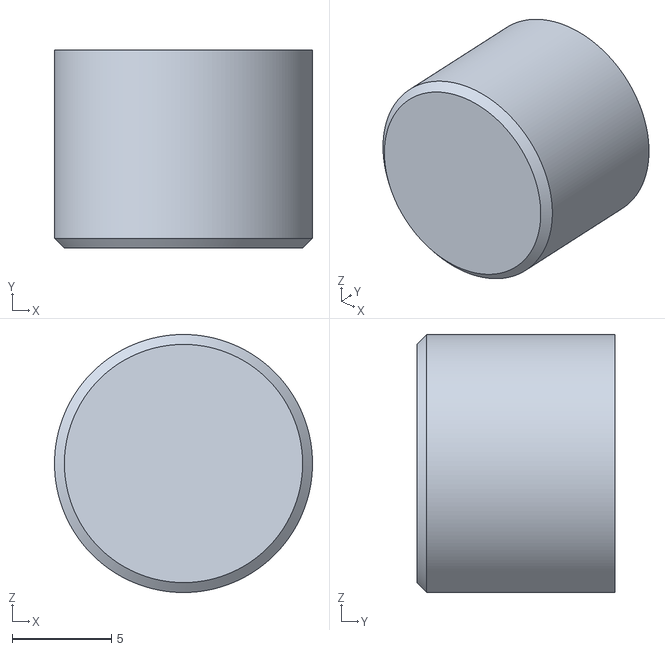
[picture p96: CAD file, 2024-03-30]
hardware-mechanical/cane/koncowka z miejscem na magnes neodymowy 7x7x3.stl
13.0 x 10.0 x 13.0
