lukasznowarkiewicz/3dCane/hardware-mechanical/cane/TRZYMACZ PCB 10 mm.stl

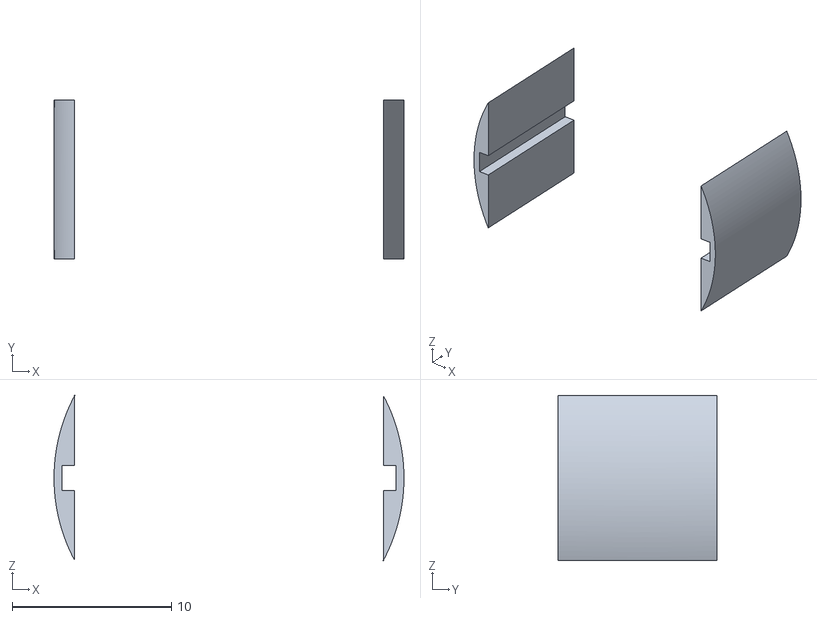
[picture p97: CAD file, 2024-03-30]
hardware-mechanical/cane/TRZYMACZ PCB 10 mm.stl
22.0 x 10.0 x 10.4
