lukasznowarkiewicz/3dCane/hardware-mechanical/cane/koncowka do laski - zaokraglona.stl

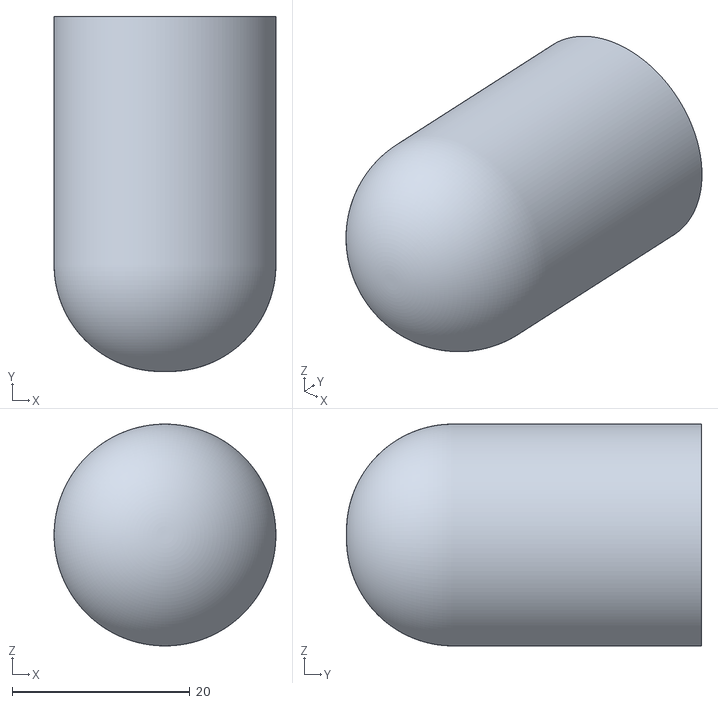
[picture p98: CAD file, 2024-03-30]
hardware-mechanical/cane/koncowka do laski - zaokraglona.stl
25.0 x 40.0 x 25.0
