lukasznowarkiewicz/3dCane/imagesAndVideos/assumptions_cane_construction2.png

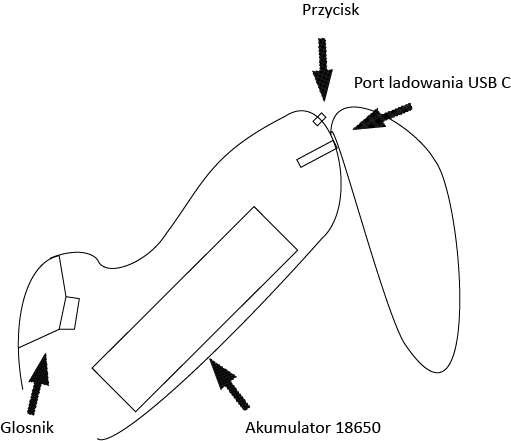
imagesAndVideos/assumptions_cane_construction2.png
