lukasznowarkiewicz/3dCane/imagesAndVideos/assumptions_cane_construction.png

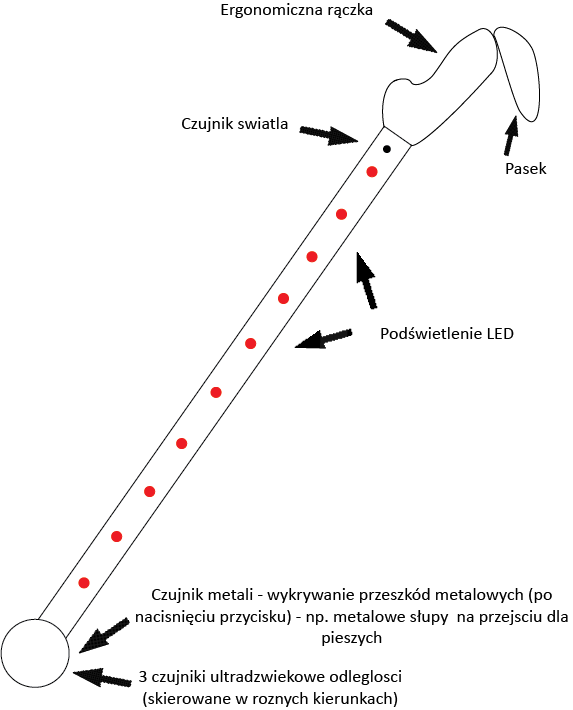
imagesAndVideos/assumptions_cane_construction.png
