lukasznowarkiewicz/3dCane/imagesAndVideos/vibration_motor_testing.JPG

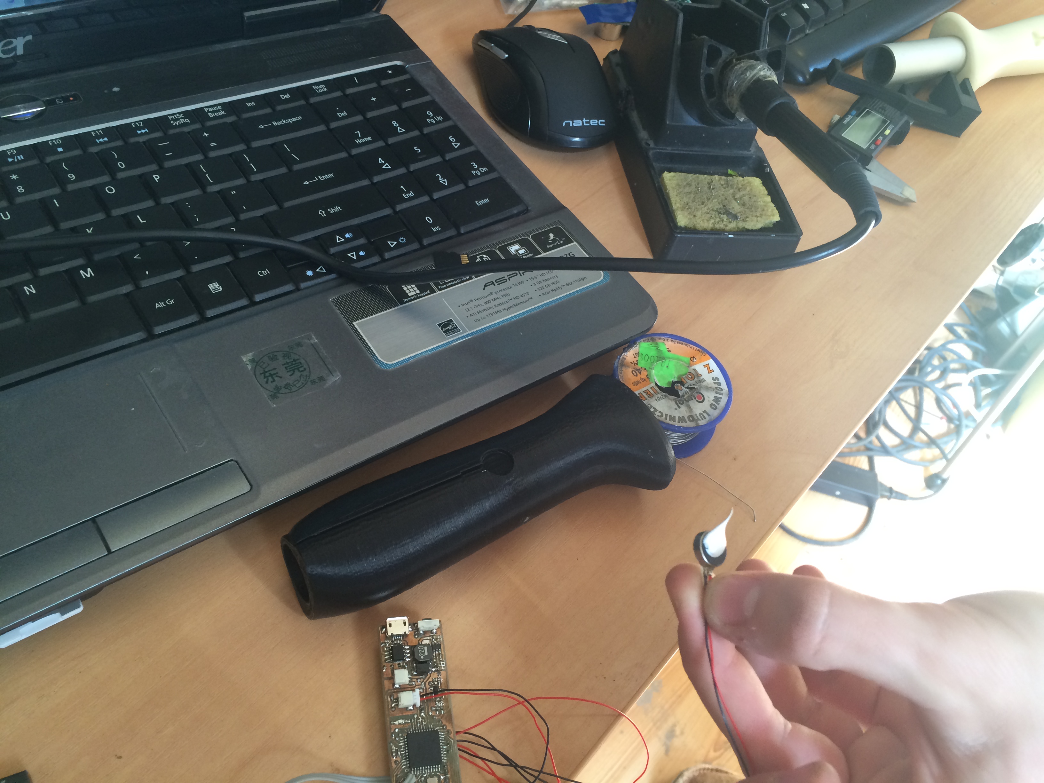
imagesAndVideos/vibration_motor_testing.JPG
